cristianghsandu/hass-esp32-ac/src/config.h

#define ENABLE_IR 1

#include "wifi_config.h"

static const char *TAG = "ac_control";

// Config
const int SEND_PIN = 26;
const int BUTTON_PIN = 12;
const int DHT22_PIN = 14;

// high, low, high, low, ...
const int data_ac[344] = {9120, -4592, 555, -1745, 555, -1745, 555, -555, 555, -555, 555, -555, 555, -555, 555, -555, 555, -1745, 555, -555, 555, -1745, 555, -1745, 555, -555, 555, -555, 555, -555, 555, -555, 555, -555, 555, -555, 555, -555, 555, -1745, 555, -555, 555, -555, 555, -555, 555, -555, 555, -555, 555, -555, 555, -1745, 555, -555, 555, -555, 555, -555, 555, -1745, 555, -1745, 555, -555, 555, -555, 555, -555, 555, -555, 555, -555, 555, -555, 555, -555, 555, -555, 555, -555, 555, -555, 555, -555, 555, -555, 555, -555, 555, -555, 555, -555, 555, -555, 555, -555, 555, -8085, 555, -1745, 555, -555, 555, -555, 555, -555, 555, -555, 555, -555, 555, -555, 555, -1745, 555, -555, 555, -555, 555, -1745, 555, -555, 555, -1745, 555, -1745, 555, -555, 555, -555, 555, -555, 555, -555, 555, -555, 555, -555, 555, -555, 555, -555, 555, -555, 555, -555, 555, -555, 555, -555, 555, -555, 555, -555, 555, -555, 555, -555, 555, -555, 555, -555, 555, -555, 555, -555, 555, -555, 555, -555, 555, -555, 555, -555, 555, -555, 555, -555, 555, -555, 555, -555, 555, -555, 555, -555, 555, -555, 555, -555, 555, -555, 555, -555, 555, -555, 555, -555, 555, -555, 555, -555, 555, -555, 555, -555, 555, -555, 555, -555, 555, -1745, 555, -1745, 555, -555, 555, -555, 555, -1745, 555, -555, 555, -1745, 555, -1745, 555, -8064, 555, -555, 555, -555, 555, -555, 555, -555, 555, -555, 555, -555, 555, -555, 555, -555, 555, -1745, 555, -555, 555, -555, 555, -555, 555, -555, 555, -555, 555, -555, 555, -555, 555, -555, 555, -555, 555, -555, 555, -555, 555, -555, 555, -555, 555, -555, 555, -555, 555, -555, 555, -555, 555, -555, 555, -555, 555, -555, 555, -555, 555, -555, 555, -555, 555, -555, 555, -555, 555, -555, 555, -555, 555, -555, 555, -555, 555, -555, 555, -555, 555, -555, 555, -555, 555, -555, 555, -555, 555, -555, 555, -555, 555, -555, 555, -555, 555, -1745, 555, -555, 555, -555, 555, -555, 555, -555, 555, -555, 555, -555, 555, -555, 555, 0};
const int data_ac_len = 343;
